djbouns/FapDan-s/Plan 3D/Piece B.STL

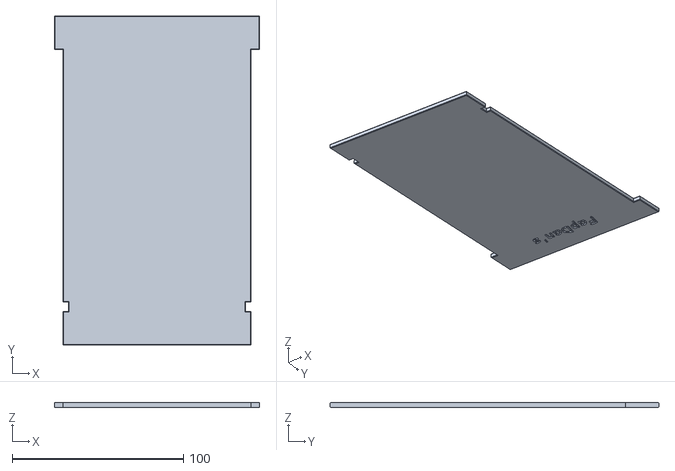
[picture p16: CAD file, 2021-02-21]
Plan 3D/Piece B.STL
120.0 x 192.3 x 3.00
