djbouns/FapDan-s/Plan 3D/Piece D haut auto V3.STL

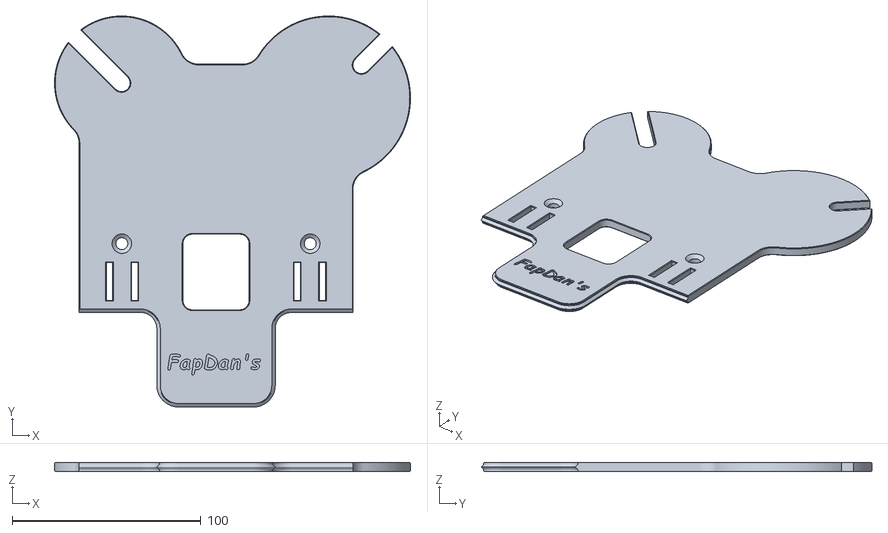
[picture p17: CAD file, 2021-02-21]
Plan 3D/Piece D haut auto V3.STL
188.4 x 206.9 x 5.00
