djbouns/FapDan-s/Plan 3D/Base controleur.STL

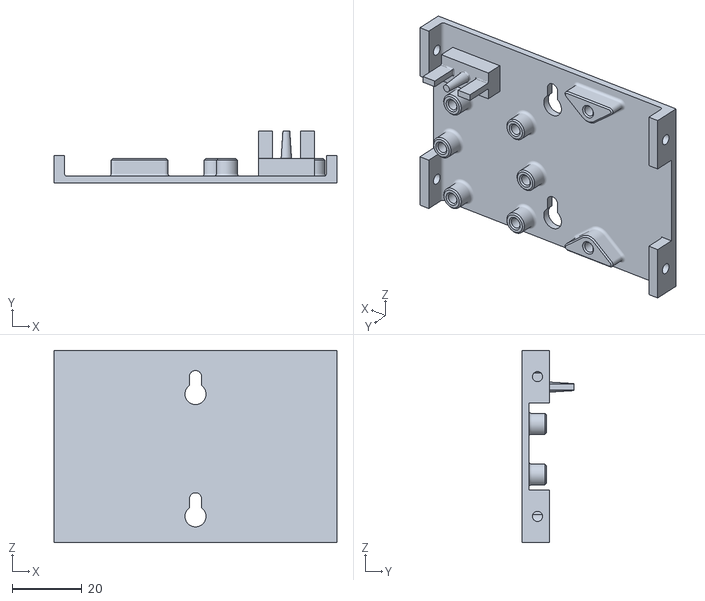
[picture p18: CAD file, 2021-02-21]
Plan 3D/Base controleur.STL
81.0 x 15.0 x 55.0
