djbouns/FapDan-s/Plan 3D/Support.STL

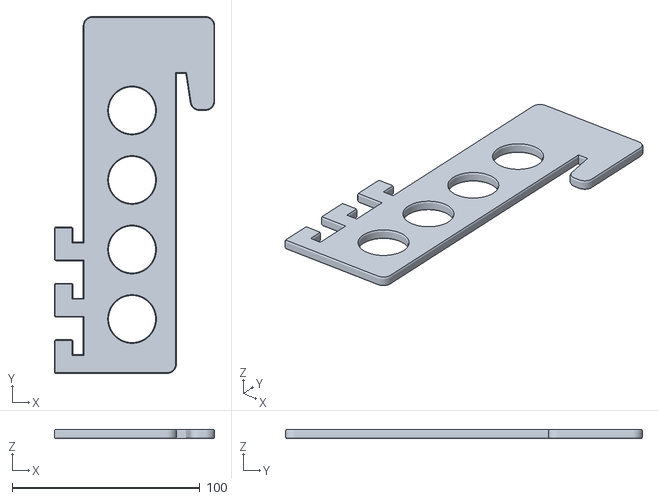
[picture p19: CAD file, 2021-02-21]
Plan 3D/Support.STL
85.4 x 190.0 x 5.00
