djbouns/FapDan-s/Plan 3D/Vis rouleaux M6.STL

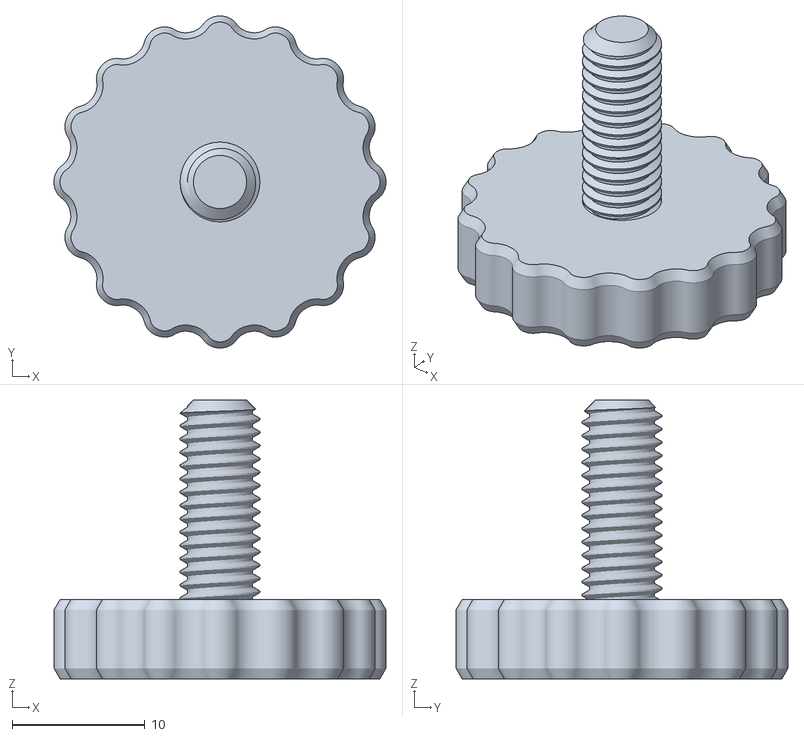
[picture p20: CAD file, 2021-02-21]
Plan 3D/Vis rouleaux M6.STL
25.0 x 25.0 x 21.0
