djbouns/FapDan-s/Plan 3D/Protecteur flotteur.STL

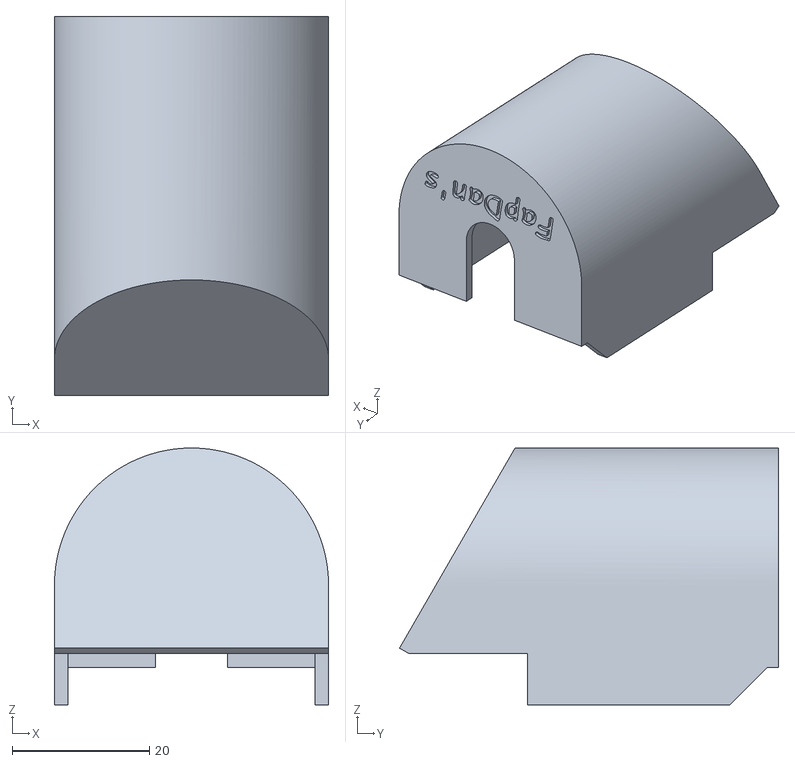
[picture p21: CAD file, 2021-02-21]
Plan 3D/Protecteur flotteur.STL
40.0 x 55.3 x 37.5
