djbouns/FapDan-s/Plan 3D/Rouleau papier lave V2.STL

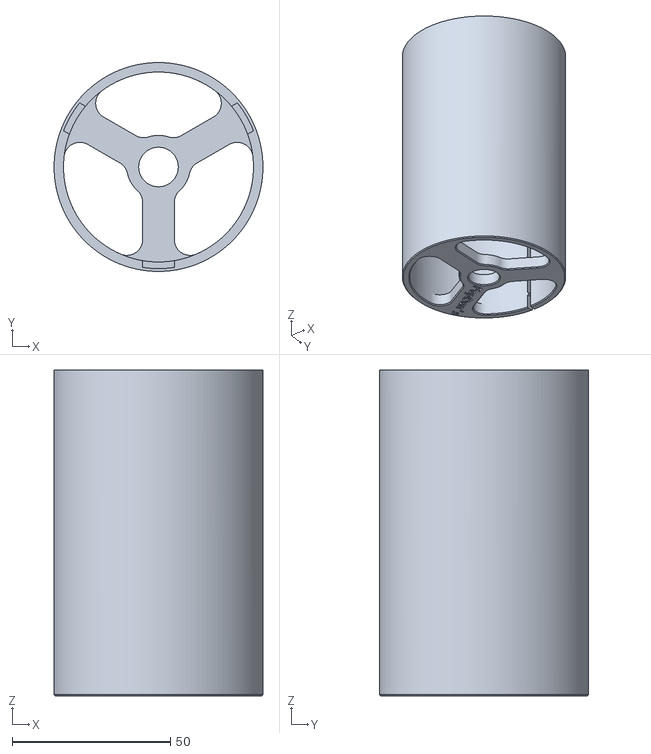
[picture p22: CAD file, 2021-02-21]
Plan 3D/Rouleau papier lave V2.STL
66.0 x 66.0 x 103.0
