djbouns/FapDan-s/Plan 3D/Rouleau papier neuf.STL

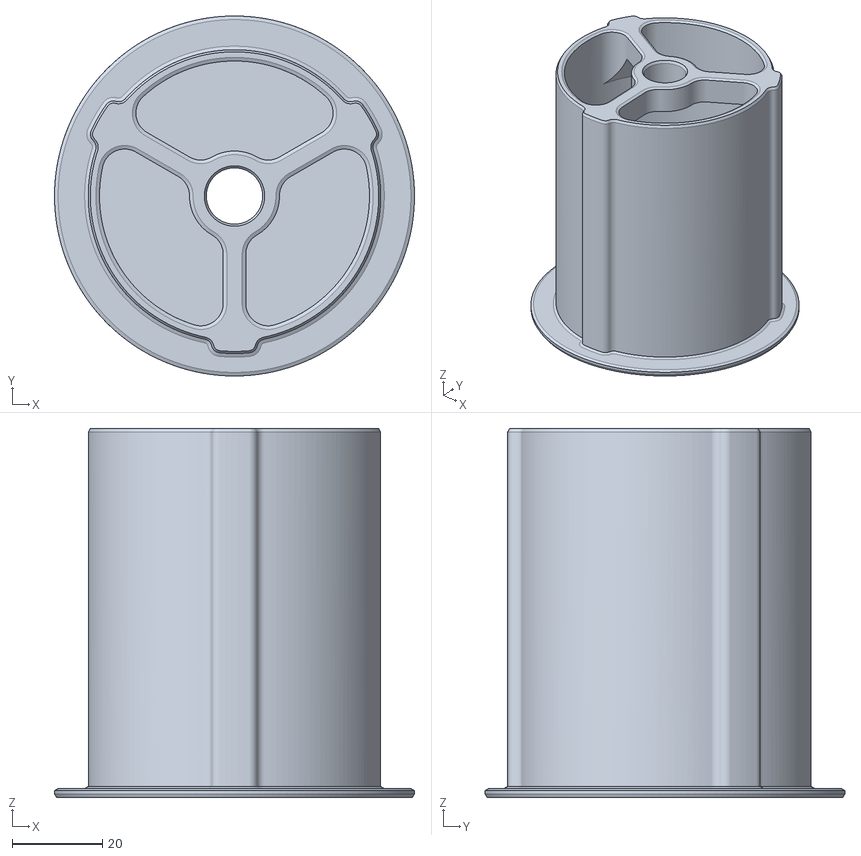
[picture p23: CAD file, 2021-02-21]
Plan 3D/Rouleau papier neuf.STL
80.0 x 80.0 x 82.0
