djbouns/FapDan-s/Plan 3D/Piece A haut auto V2.STL

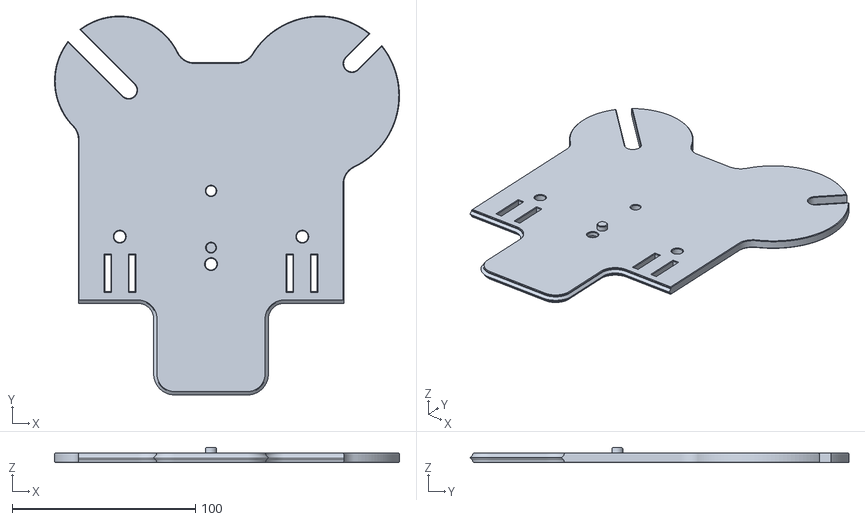
[picture p24: CAD file, 2021-02-21]
Plan 3D/Piece A haut auto V2.STL
188.4 x 206.9 x 8.00
