djbouns/FapDan-s/Plan 3D/Piece A bas.STL

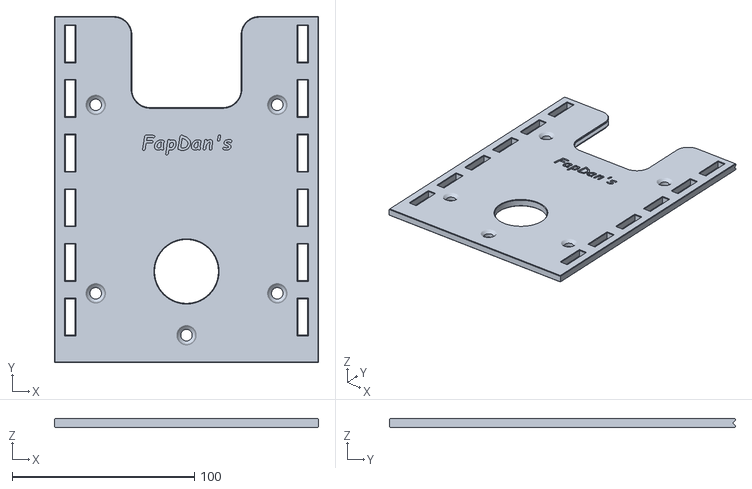
[picture p25: CAD file, 2021-02-21]
Plan 3D/Piece A bas.STL
145.0 x 190.0 x 5.00
