djbouns/FapDan-s/Plan 3D/Vis support capteur niveau M6.STL

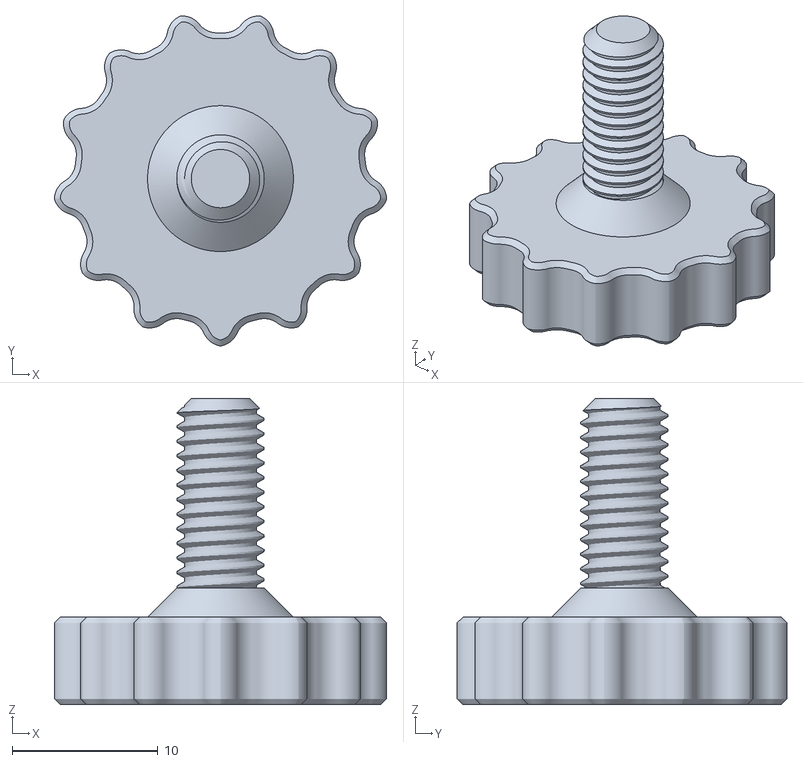
[picture p26: CAD file, 2021-02-21]
Plan 3D/Vis support capteur niveau M6.STL
22.8 x 22.6 x 21.0
