djbouns/FapDan-s/Plan 3D/Ecrou support capteur niveau M6.STL

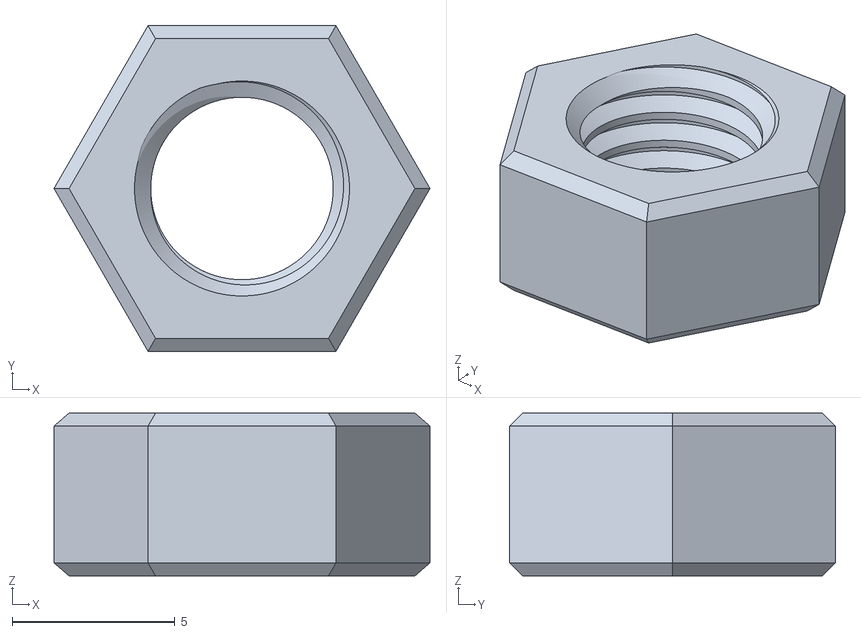
[picture p27: CAD file, 2021-02-21]
Plan 3D/Ecrou support capteur niveau M6.STL
11.5 x 10.0 x 5.00
