djbouns/FapDan-s/Plan 3D/Grille A.STL

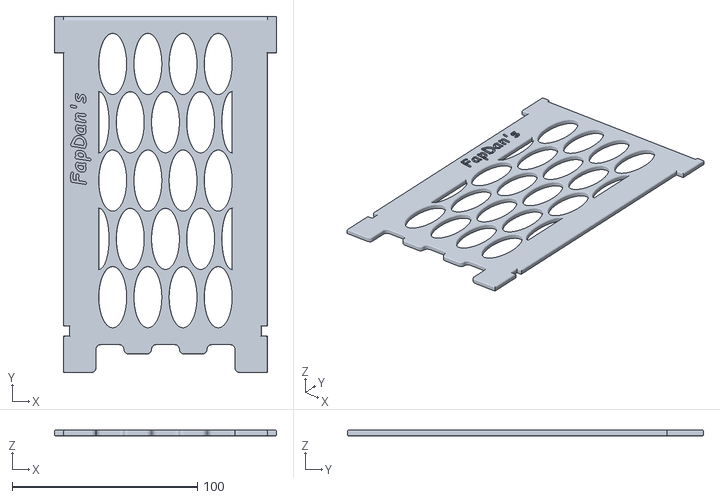
[picture p28: CAD file, 2021-02-21]
Plan 3D/Grille A.STL
120.0 x 192.3 x 3.00
