djbouns/FapDan-s/Plan 3D/Centre rouleau papier lave V2.STL

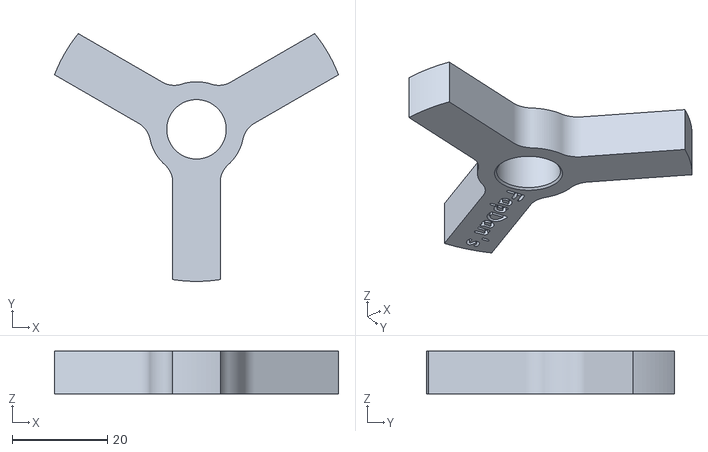
[picture p29: CAD file, 2021-02-21]
Plan 3D/Centre rouleau papier lave V2.STL
59.7 x 52.1 x 9.00
