djbouns/FapDan-s/Plan 3D/Couvercle moteur.STL

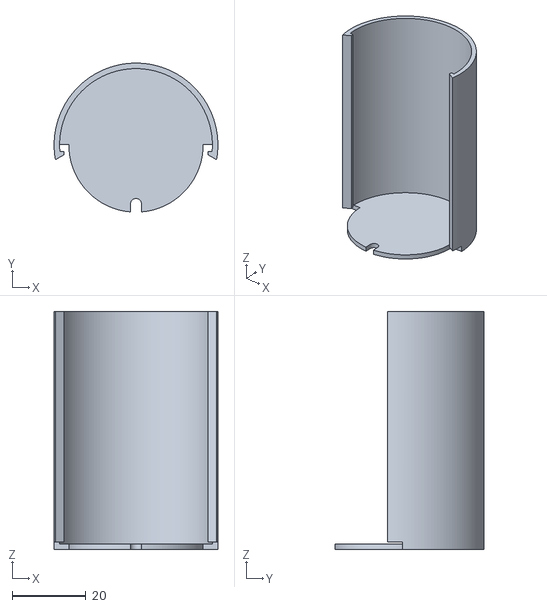
[picture p30: CAD file, 2021-02-21]
Plan 3D/Couvercle moteur.STL
44.4 x 40.3 x 64.5
