djbouns/FapDan-s/Plan 3D/Protecteur flotteur V2.STL

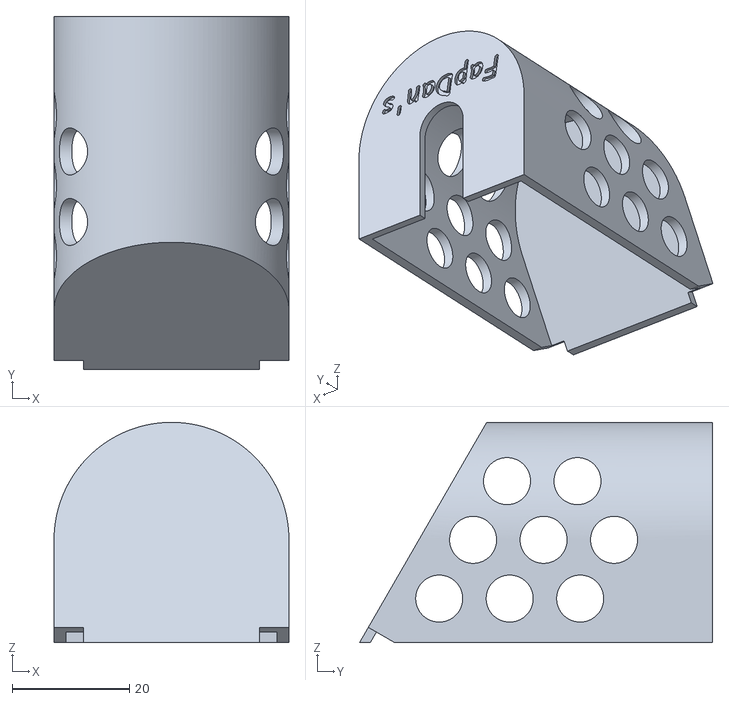
[picture p31: CAD file, 2021-02-21]
Plan 3D/Protecteur flotteur V2.STL
40.0 x 60.1 x 37.5
